banthony42/projet_marvin/raspberry/marvin_code/sources/main.c

#include <stdio.h>
#include <unistd.h>
#include <string.h>
#include "marvin.h"
#include <time.h>
#include "server.h"
#include <stdlib.h>

int	main(int argc, char **argv, char **env)
{

	t_marvin marvin;

	fd_set rdfs;
	printf("Lancement du Programme...\n");
	marvin_init(&marvin);
	marvin_options(&marvin, argc, argv);

	if (IS_DEBUG(marvin.options))
		printf("verbose mode\n");
	if (marvin.options == OPTION_ERROR)
	{
		printf("Invalid Arguments\n");
		printf("EXIT\n");
		return (-1);
	}
	marvin_init_uart(&marvin);
	marvin.sock = init_connection();	
	marvin.max = marvin.sock;
	srand(time(NULL));
	if (IS_DEBUG(marvin.options))
		printf("Init Socket\n");
		while (1)
		{
			set_and_clear(&marvin, &rdfs);
			if(new_client(&marvin, &rdfs))
			{
				read_input(&marvin);	
				char empty[2048];
				while (read(marvin.fd_uart, empty, 2047) > 0);
				marvin_destruct_receive(marvin.r_begin);
				marvin.nbrordres_receives = 0;
				marvin.r_begin = NULL;
				bzero(marvin.tab, sizeof(marvin.tab));
				bzero(marvin.receive, sizeof(marvin.receive));
				bzero(marvin.send, sizeof(marvin.send));
				continue ;
			}
			read_input(&marvin);	
			if (!(strcmp(marvin.send, "exit")))
				break;
			send_data(&marvin);
			receive_message(&marvin);
			if (marvin.nbrordres_receives >= MAX_ORDRE)
			{
				if (IS_DEBUG(marvin.options))
					printf("%d ordres ont ete recus\n", MAX_ORDRE);
				int ordre = 0;

				ordre = marvin_tri_ordre(marvin.r_begin, &marvin);
				if (ordre == 0)
				{
					if (IS_DEBUG(marvin.options))
						printf ("Aucun ordre valable\n");
				}
				else
				{
					if (IS_DEBUG(marvin.options))
						printf("L'ordre numero %d a ete recu \n", ordre);
					marvin_launch_order(&marvin, ordre);
				}
				//receive_message(&marvin);
				//clear uart
				char empty[2048];
				while (read(marvin.fd_uart, empty, 2047) > 0);
				marvin_destruct_receive(marvin.r_begin);
				marvin.nbrordres_receives = 0;
				marvin.r_begin = NULL;
				bzero(marvin.tab, sizeof(marvin.tab));
				bzero(marvin.receive, sizeof(marvin.receive));
				bzero(marvin.send, sizeof(marvin.send));
			}
		}
		close(marvin.fd_uart);
		clear_clients(marvin.clients, marvin.actual);
		end_connection(marvin.sock);
	return (0);
}
