banthony42/projet_marvin/POC/MPLAB/marvin_v02.X/tools.c

#include "types.h"
#include "tools.h"

u32		ft_atoi(u8 *str)
{
    u32 nb;
    u32 dizaine;
    u32 signe;

    nb = 0;
    dizaine = 10;
    signe = -1;
    while (*str == '\t' || *str == '\n' || *str == '\v'
                    || *str == '\f' || *str == '\r' || *str == ' ')
            str++;
    if (*str == 45 || *str == 43)
    {
            if (*str == 45)
                    signe *= -1;
            str++;
    }
    while (*str >= 48 && *str <= 57)
    {
            nb *= dizaine;
            nb -= (*str - 48);
            str++;
    }
    return (nb * signe);
}


/*
 * Delay en ms
 * Param1: le nbr de ms a attendre
 */

void    marvin_tempo(u32 tempo)
{
    u32 tmp;

    tmp = marvin.counter1;
    while (marvin.counter1 < tmp + tempo);
}

/*
 * Fonction map (c.f arduino, Return un y compris dans [out_min ; out_max] proportionelle a x compris entre [in_min ; in_max]
 * Param1: Valeur x recus comprise entre in_min et in_max
 * Param2: Valeur minimal de x
 * Param3: Valeur maximal de x
 * Param4: Valeur minimal de y (y etant la valeur du return)
 * Param5: Valeur maximal de y (y etant la valeur du return)
 */
u32 map(u32 x, u32 in_min, u32 in_max, u32 out_min, u32 out_max)
{
    return (((x - in_min) * (out_max - out_min)) / ((in_max - in_min) + out_min)); // Code de la fonction Map Arduino
}

/*
 * Retourne la medianne d'une serie de valeur
 * Param1: tableau de valeurs, le tableau doit etre trier par ordre croissant
 * Param2 : Taille du taleau
 * Return : La medianne
 */
u16 marvin_calcul_median(u16 *tab, u8 size)
{
  u8 index;
  u8 nbrzero = 0;

  while (*(tab + nbrzero) == 0 && nbrzero < size)   // Pour pallier au bug du Sonar on va ignorer les zeros;
      ++nbrzero;
  index = (size - nbrzero +  1) / 2 ;
  if (index  > size)
      return (0);
  if ((size + 1 ) % 2 == 0)
    return (*(tab + index -1 + nbrzero));           // -1 car on commenc a comtper a partir de zero;
  else
   return ( (*(tab + index - 1 +nbrzero) + *(tab + index +nbrzero)) / 2) ;
}


/*
 * fonction qui tri par insertion
 * Param1: tableau qui contiendras les valeurs triees
 * Param2: taille du tableau
 * Param3 valeur a inserer
 */
u16 marvin_tri_insertion(u16 *tab, u8 size, u16 valeur)
{
  u16 *pos;

  if (valeur == 6066)               // Test si erreur
      return (6066);                // Return erreur
  while (size && *tab < valeur)
  {
    ++tab;
    --size;
  }
  pos = tab;
  if (size)
  {
    while (size)
    {
      ++tab;
      --size;
    }
    while (tab > pos)
    {
      *tab = *(tab - 1);
      tab--;
    }
  }
  *pos = valeur;
  return (1);
}
