banthony42/projet_marvin/POC/MPLAB/marvin_v02.X/tools.h

/*
 * File:   tools.h
 * Author: Amulin, Aodren, Banthony, Tbeauman.
 *
 * Created on June 2, 2016, 7:02 PM
 */

#ifndef TOOLS_H
#define	TOOLS_H
#include "types.h"

u32     map(u32 x, u32 in_min, u32 in_max, u32 out_min, u32 out_max);
u16     marvin_tri_insertion(u16 *tab, u8 size, u16 valeur);
u16     marvin_calcul_median(u16 *tab, u8 size);
void    marvin_tempo(u32 tempo);
u32     marvin_itoa(u8 *str);

#endif	/* TOOLS_H */
