banthony42/projet_marvin/POC/MPLAB/marvin_v02.X/configbits.c

// PIC32MX270F256B Configuration Bit Settings

// 'C' source line config statements

#include <xc.h>

// DEVCFG3
// USERID = No Setting
#pragma config PMDL1WAY = ON            // Peripheral Module Disable Configuration (Allow only one reconfiguration)
#pragma config IOL1WAY = ON             // Peripheral Pin Select Configuration (Allow only one reconfiguration)
#pragma config FUSBIDIO = OFF            // USB USID Selection (Controlled by the USB Module)
#pragma config FVBUSONIO = OFF           // USB VBUS ON Selection (Controlled by USB Module)

// DEVCFG2
#pragma config FPLLIDIV = DIV_12        // PLL Input Divider (12x Divider)
#pragma config FPLLMUL = MUL_24         // PLL Multiplier (24x Multiplier)
#pragma config UPLLIDIV = DIV_12        // USB PLL Input Divider (12x Divider)
#pragma config UPLLEN = OFF             // USB PLL Enable (Disabled and Bypassed)
#pragma config FPLLODIV = DIV_256       // System PLL Output Clock Divider (PLL Divide by 256)

// DEVCFG1
#pragma config FNOSC = FRC             // Oscillator Selection Bits (Fast RC Osc (FRC))
#pragma config FSOSCEN = OFF             // Secondary Oscillator Enable (Enabled)
#pragma config IESO = ON                // Internal/External Switch Over (Enabled)
#pragma config POSCMOD = OFF            // Primary Oscillator Configuration (Primary osc disabled)
#pragma config OSCIOFNC = OFF           // CLKO Output Signal Active on the OSCO Pin (Disabled)
#pragma config FPBDIV = DIV_8           // Peripheral Clock Divisor (Pb_Clk is Sys_Clk/8)
#pragma config FCKSM = CSDCMD           // Clock Switching and Monitor Selection (Clock Switch Disable, FSCM Disabled)
#pragma config WDTPS = PS1048576        // Watchdog Timer Postscaler (1:1048576)
#pragma config WINDIS = OFF             // Watchdog Timer Window Enable (Watchdog Timer is in Non-Window Mode)
#pragma config FWDTEN = OFF             // Watchdog Timer Enable (WDT Disabled (SWDTEN Bit Controls))
#pragma config FWDTWINSZ = WINSZ_25     // Watchdog Timer Window Size (Window Size is 25%)

// DEVCFG0
#pragma config JTAGEN = OFF              // JTAG Enable (JTAG Port Enabled)
#pragma config ICESEL = ICS_PGx1        // ICE/ICD Comm Channel Select (Communicate on PGEC1/PGED1)
#pragma config PWP = OFF                // Program Flash Write Protect (Disable)
#pragma config BWP = OFF                // Boot Flash Write Protect bit (Protection Disabled)
#pragma config CP = OFF                // Code Protect (Protection Disabled)
